jeremy-daily/Teensy-Crash-EDR/docs/images/2016-09-08 15.51.45.jpg

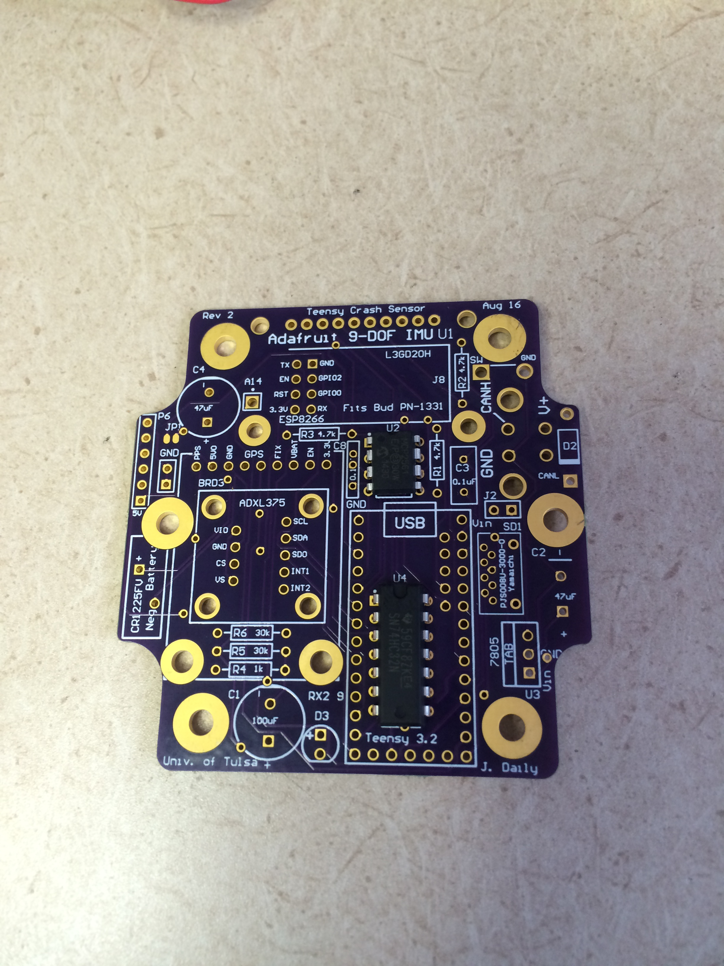
docs/images/2016-09-08 15.51.45.jpg
