jeremy-daily/Teensy-Crash-EDR/docs/images/2016-09-08 15.54.55.jpg

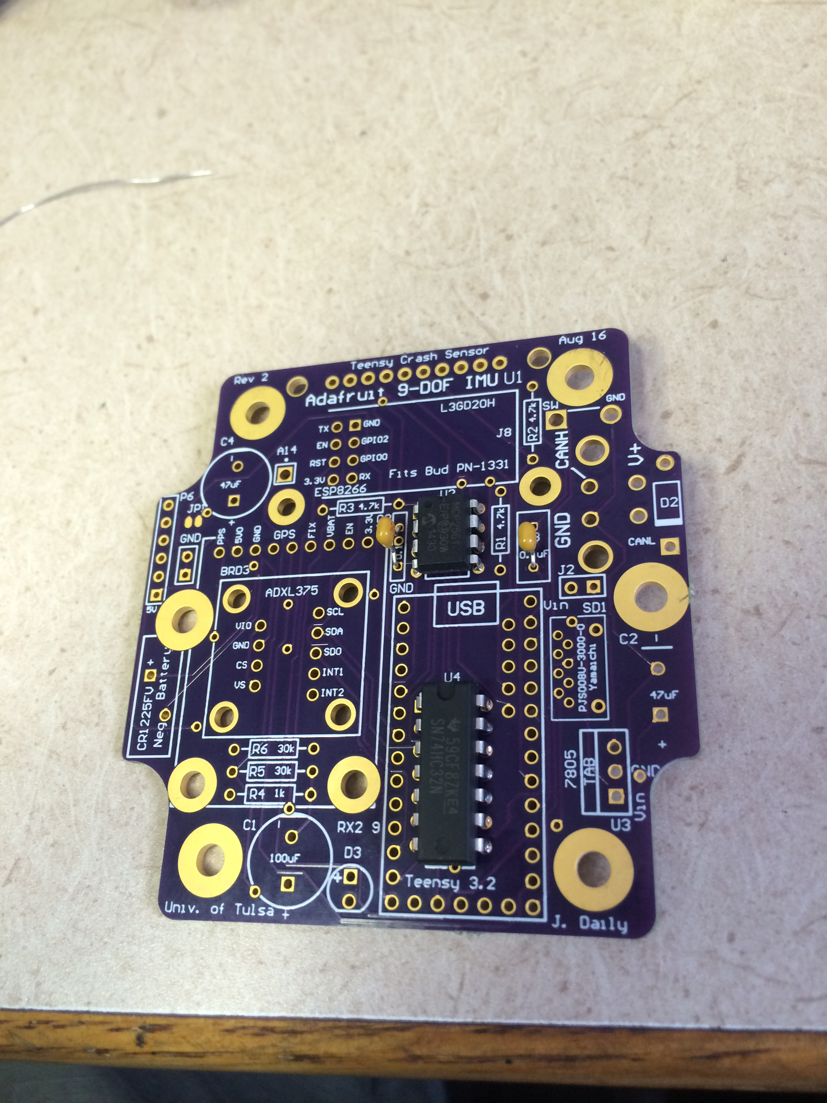
docs/images/2016-09-08 15.54.55.jpg
