jeremy-daily/Teensy-Crash-EDR/docs/images/2016-09-08 16.11.41.jpg

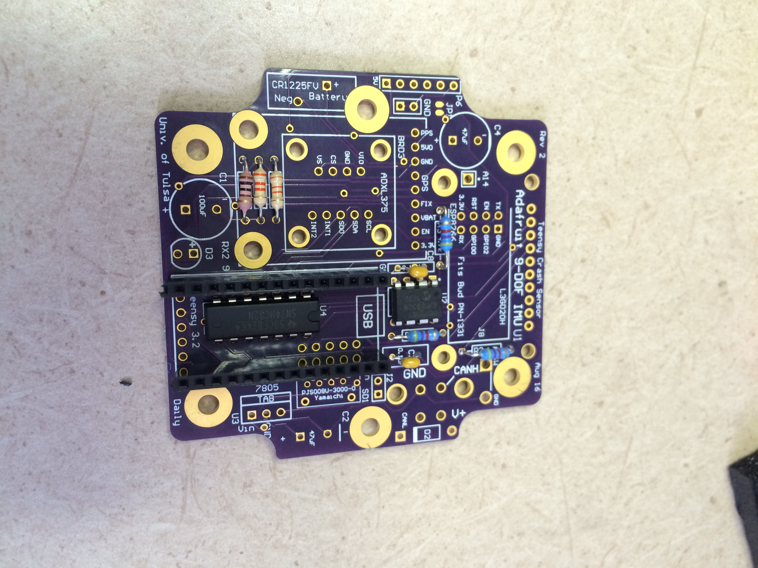
docs/images/2016-09-08 16.11.41.jpg
