jeremy-daily/Teensy-Crash-EDR/docs/images/2016-09-08 16.32.50.jpg

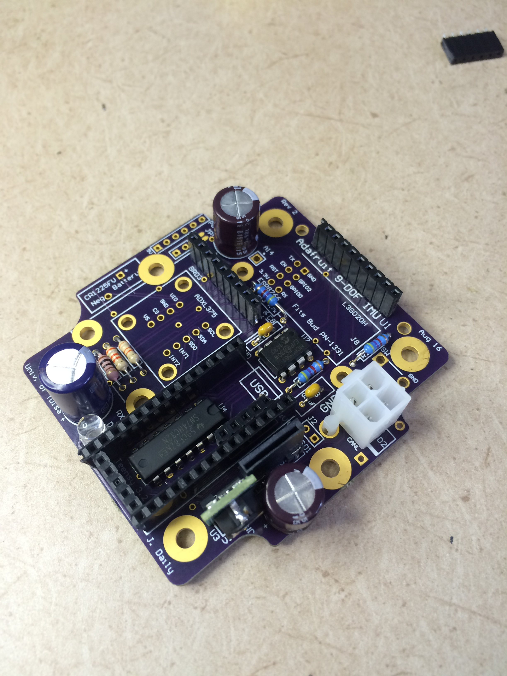
docs/images/2016-09-08 16.32.50.jpg
