jeremy-daily/Teensy-Crash-EDR/docs/images/2016-09-08 16.55.00.jpg

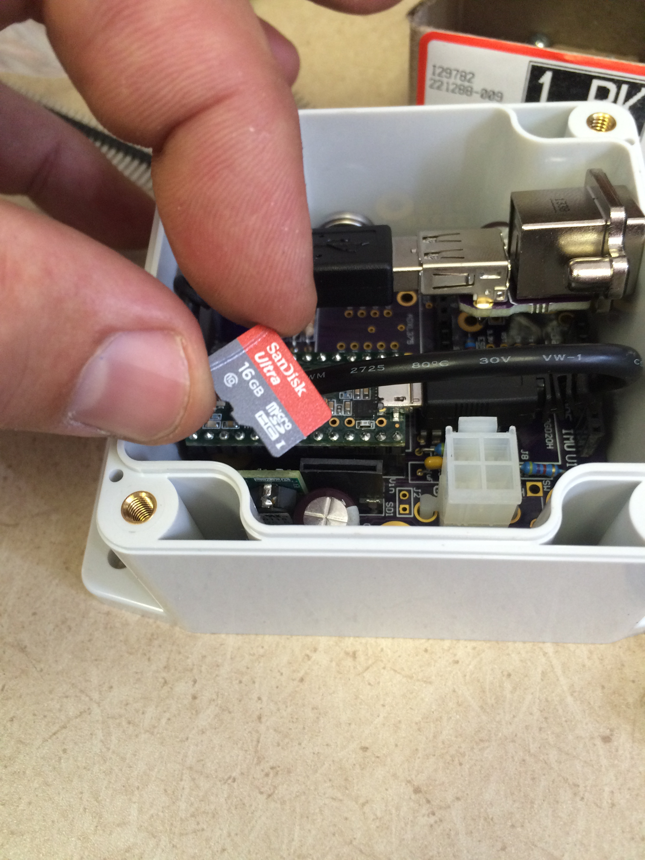
docs/images/2016-09-08 16.55.00.jpg
