jeremy-daily/Teensy-Crash-EDR/docs/images/2016-09-09 11.59.14.jpg

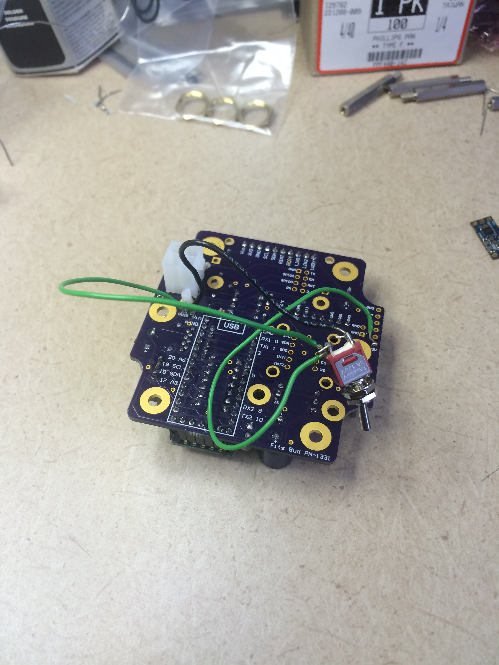
docs/images/2016-09-09 11.59.14.jpg
