jeremy-daily/Teensy-Crash-EDR/docs/images/2016-09-09 12.16.07.jpg

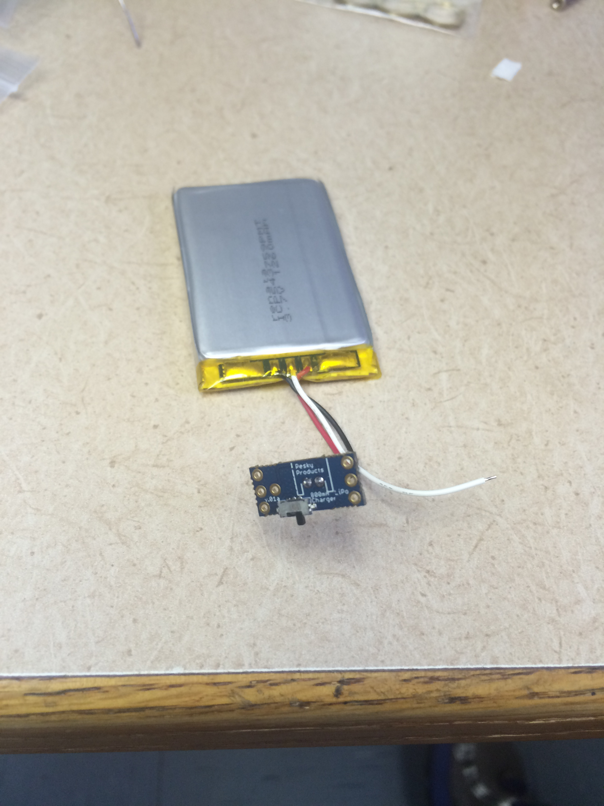
docs/images/2016-09-09 12.16.07.jpg
