jeremy-daily/Teensy-Crash-EDR/docs/images/2016-09-09 12.16.24.jpg

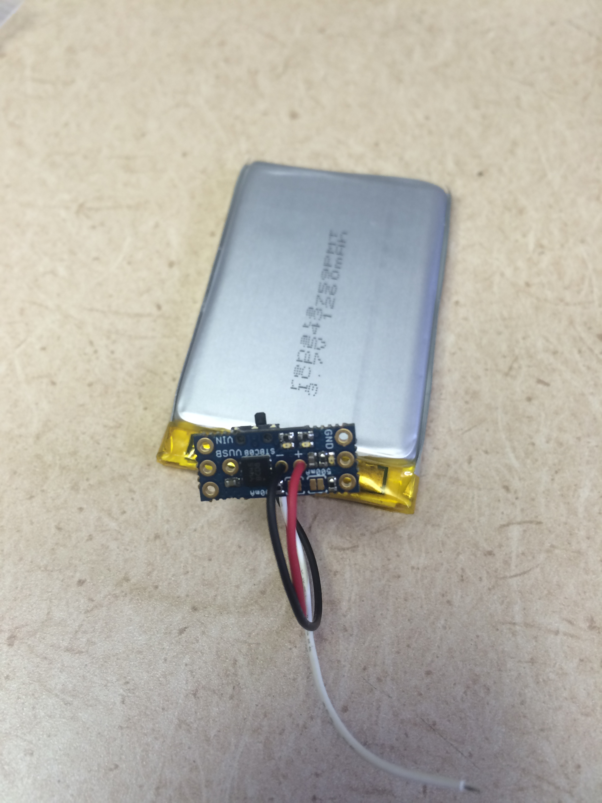
docs/images/2016-09-09 12.16.24.jpg
