jeremy-daily/Teensy-Crash-EDR/docs/images/2016-09-09 12.26.00.jpg

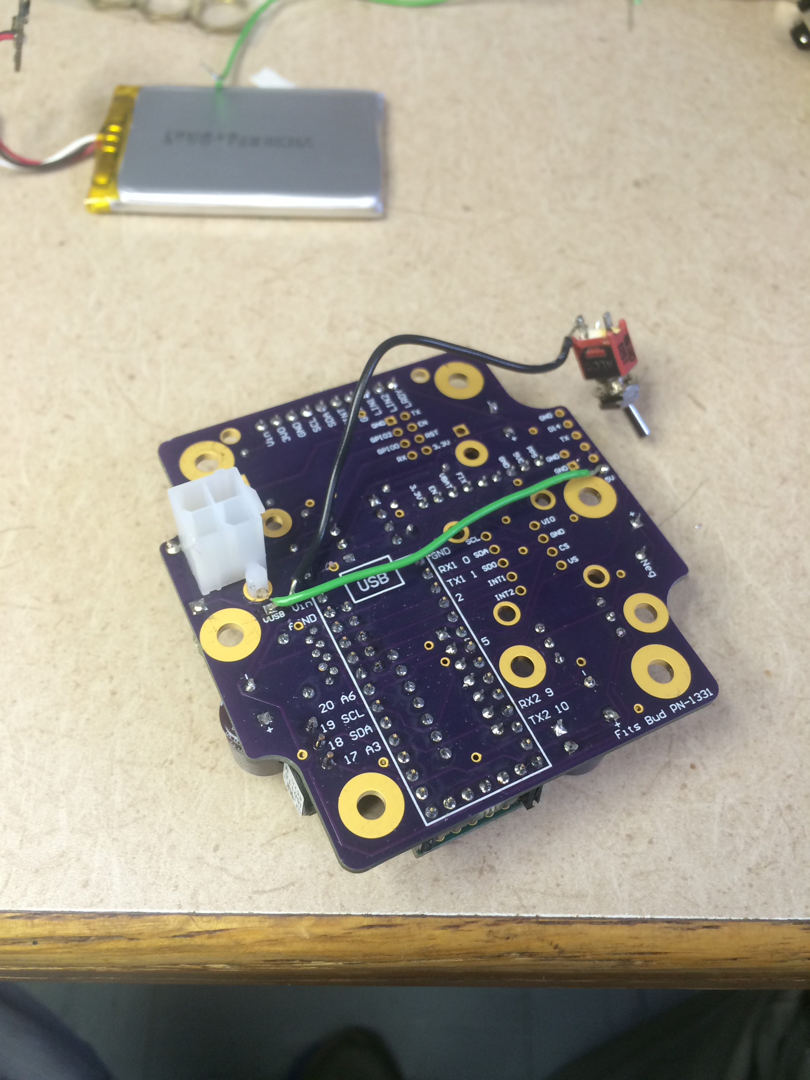
docs/images/2016-09-09 12.26.00.jpg
