jeremy-daily/Teensy-Crash-EDR/docs/images/2016-09-09 12.34.02.jpg

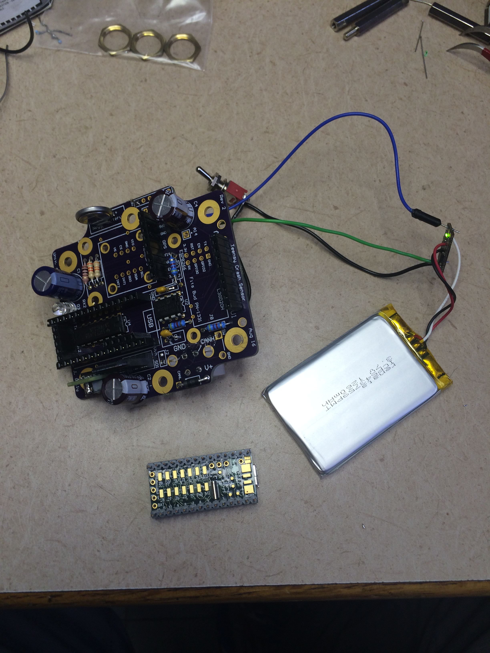
docs/images/2016-09-09 12.34.02.jpg
