jeremy-daily/Teensy-Crash-EDR/docs/images/2016-09-09 12.36.15.jpg

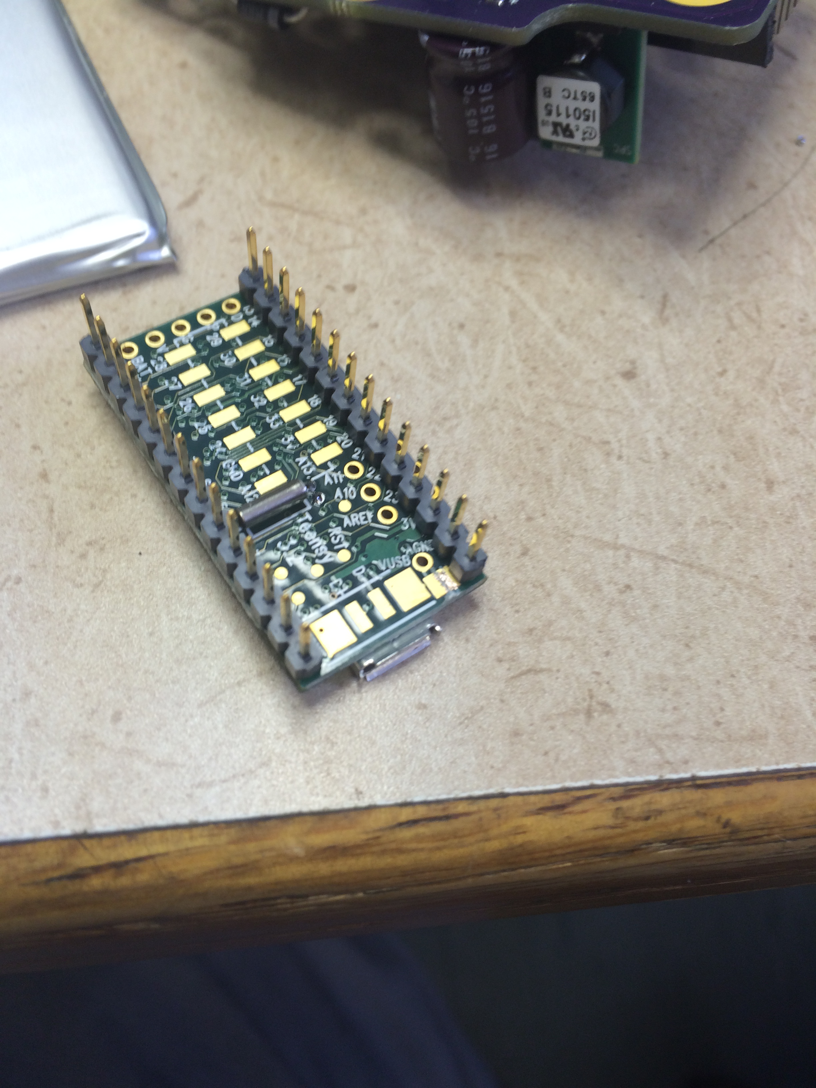
docs/images/2016-09-09 12.36.15.jpg
