jeremy-daily/Teensy-Crash-EDR/docs/images/2016-09-09 13.00.01.jpg

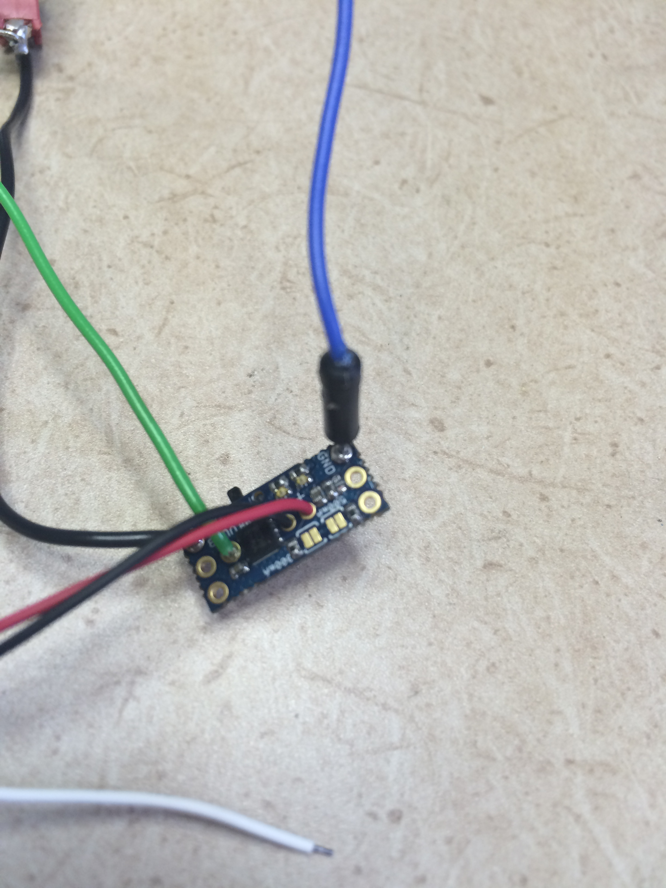
docs/images/2016-09-09 13.00.01.jpg
