jeremy-daily/Teensy-Crash-EDR/docs/images/2016-09-09 13.43.51.jpg

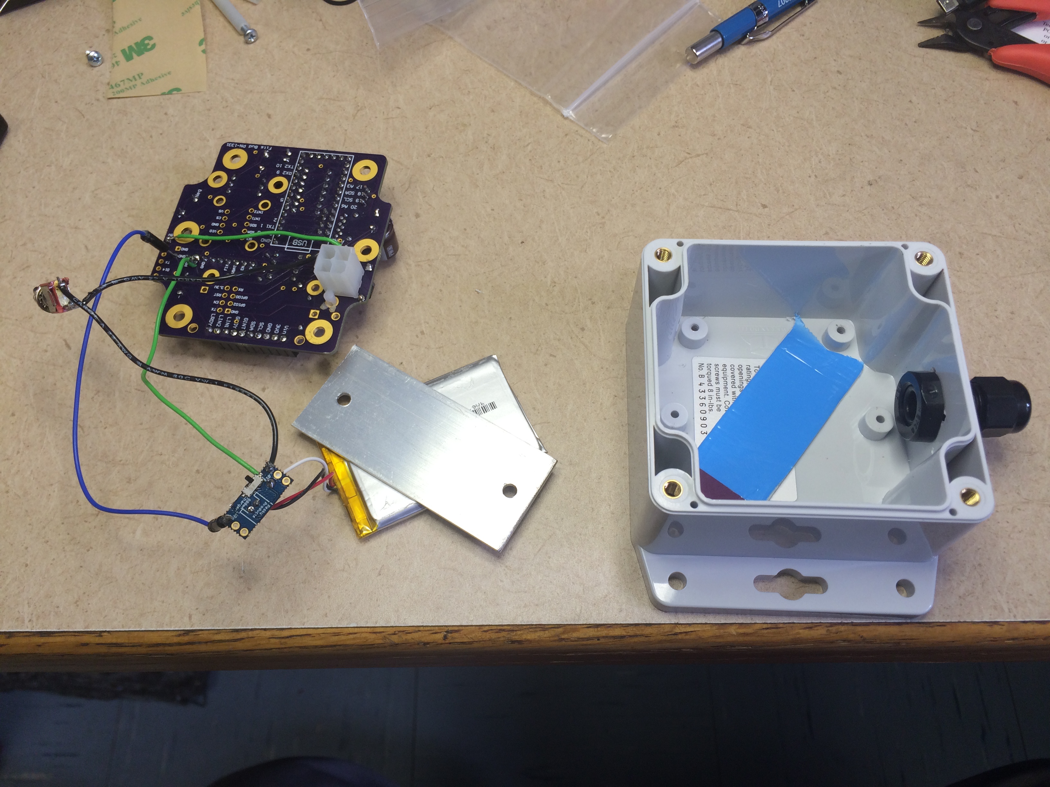
docs/images/2016-09-09 13.43.51.jpg
