jeremy-daily/Teensy-Crash-EDR/docs/images/2016-09-09 13.45.09.jpg

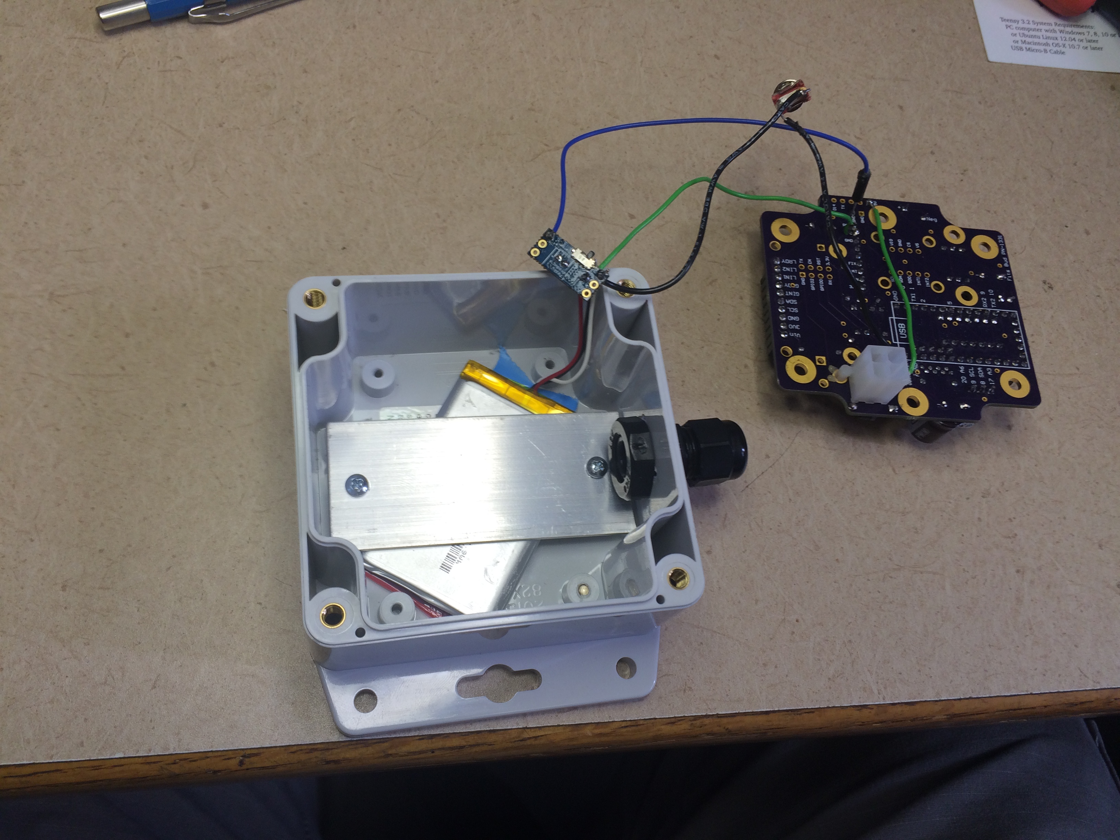
docs/images/2016-09-09 13.45.09.jpg
