jeremy-daily/Teensy-Crash-EDR/docs/images/2016-09-09 13.49.27.jpg

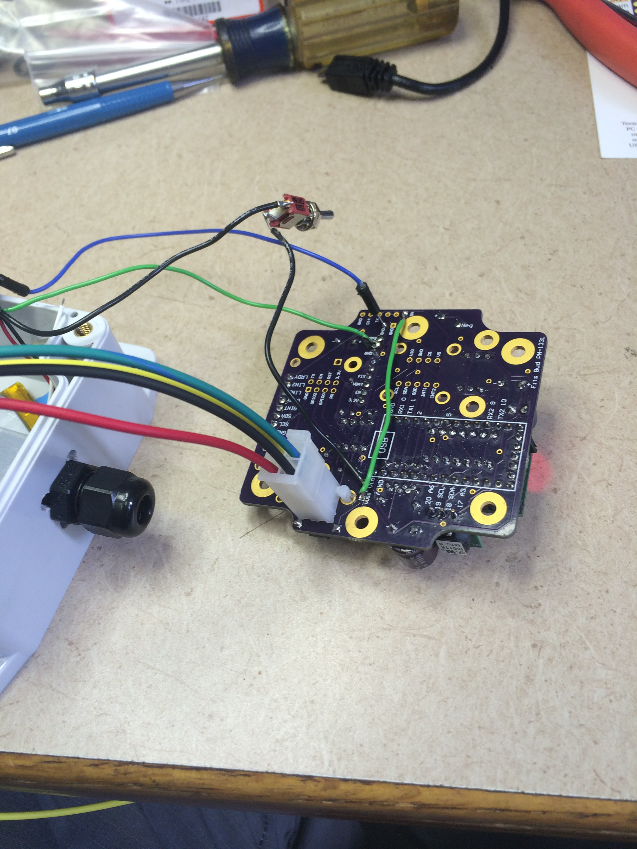
docs/images/2016-09-09 13.49.27.jpg
