jeremy-daily/Teensy-Crash-EDR/docs/images/2016-09-09 14.00.38.jpg

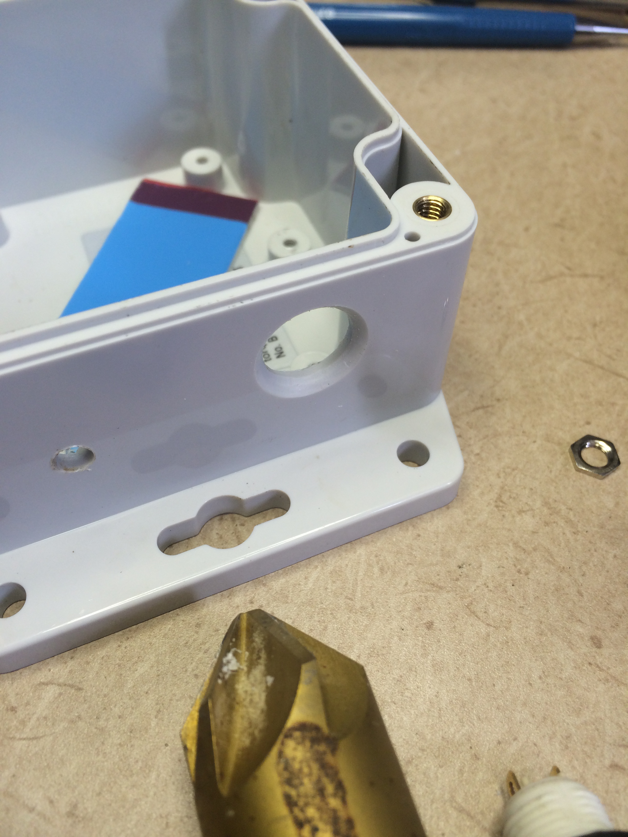
docs/images/2016-09-09 14.00.38.jpg
