jeremy-daily/Teensy-Crash-EDR/docs/images/2016-09-09 14.05.18.jpg

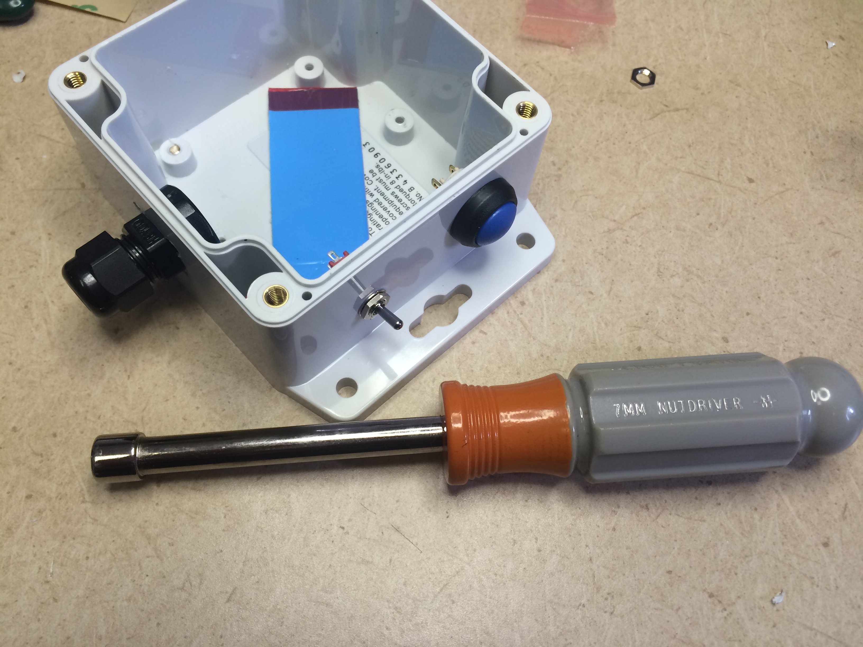
docs/images/2016-09-09 14.05.18.jpg
