jeremy-daily/Teensy-Crash-EDR/docs/images/2016-09-09 14.09.20.jpg

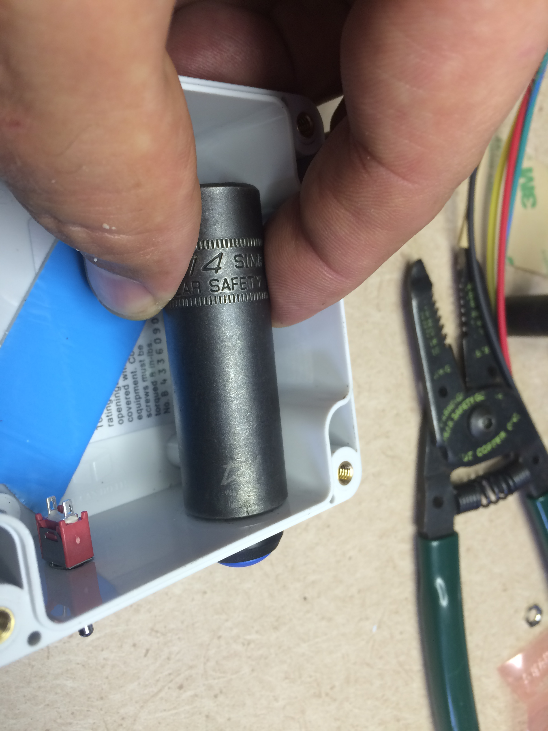
docs/images/2016-09-09 14.09.20.jpg
