jeremy-daily/Teensy-Crash-EDR/docs/images/2016-09-09 15.44.33.jpg

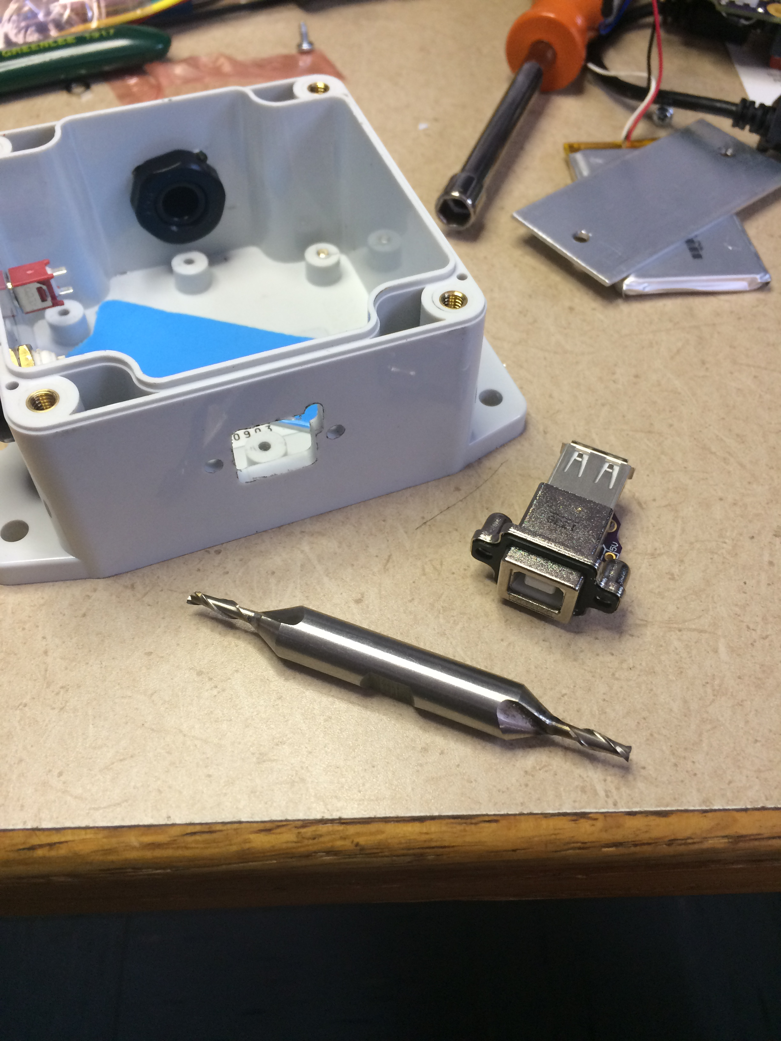
docs/images/2016-09-09 15.44.33.jpg
