jeremy-daily/Teensy-Crash-EDR/docs/images/2016-09-09 15.50.09.jpg

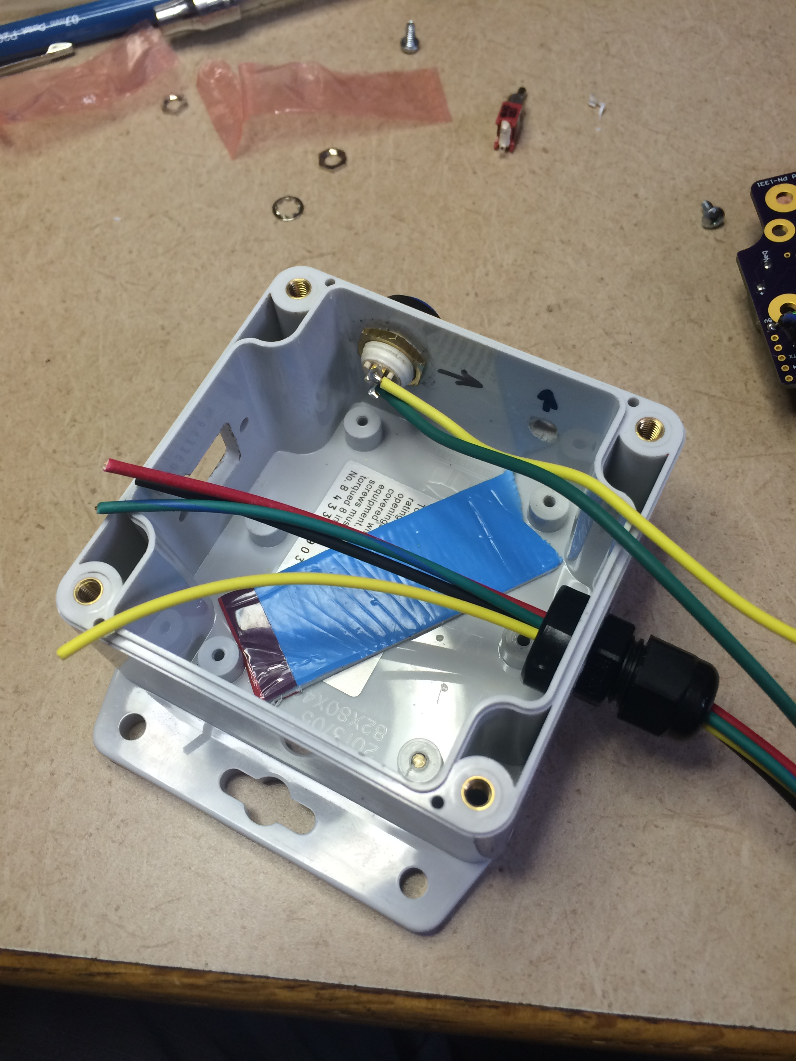
docs/images/2016-09-09 15.50.09.jpg
