jeremy-daily/Teensy-Crash-EDR/docs/images/2016-09-09 15.57.11.jpg

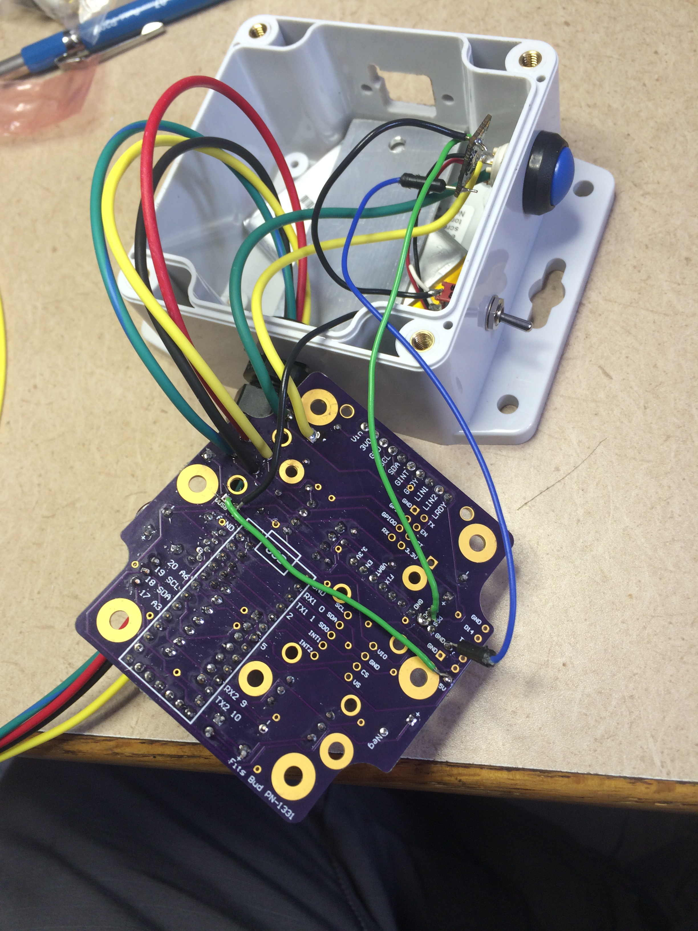
docs/images/2016-09-09 15.57.11.jpg
