jeremy-daily/Teensy-Crash-EDR/docs/images/2016-09-09 15.58.31.jpg

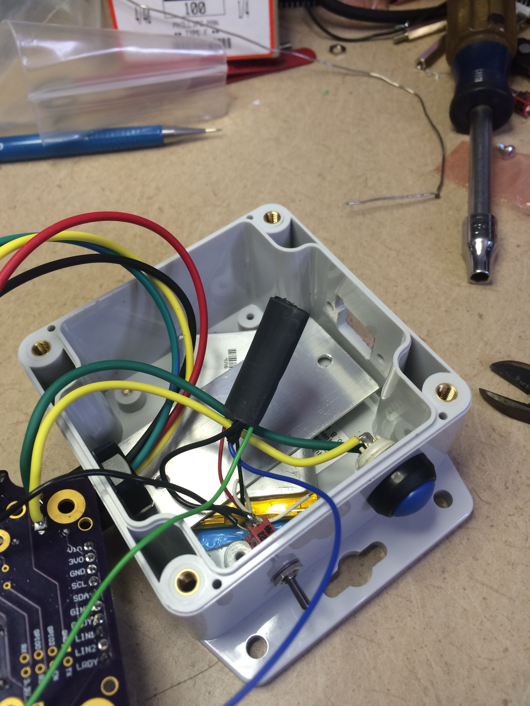
docs/images/2016-09-09 15.58.31.jpg
