jeremy-daily/Teensy-Crash-EDR/docs/images/2016-09-09 16.00.55.jpg

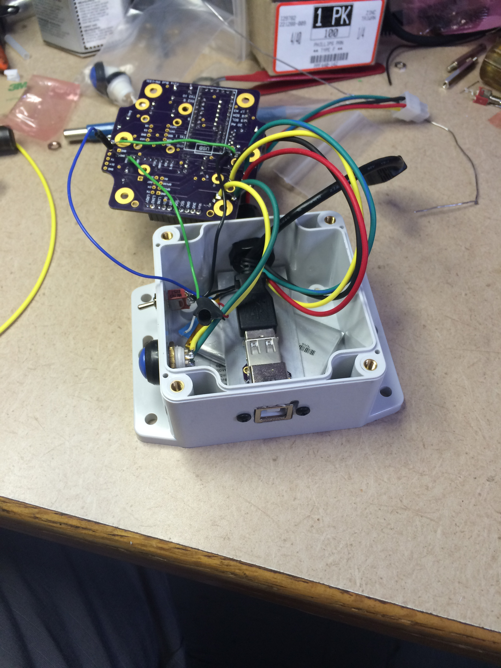
docs/images/2016-09-09 16.00.55.jpg
