jeremy-daily/Teensy-Crash-EDR/docs/images/2016-09-09 16.04.29.jpg

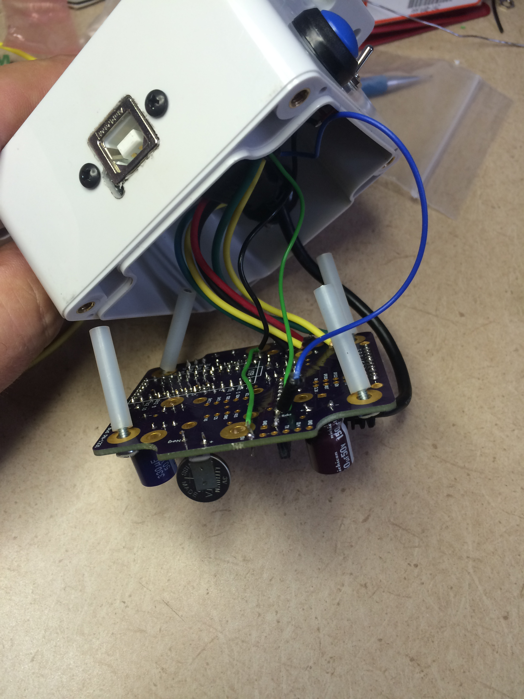
docs/images/2016-09-09 16.04.29.jpg
