jeremy-daily/Teensy-Crash-EDR/docs/images/2016-09-09 16.16.41.jpg

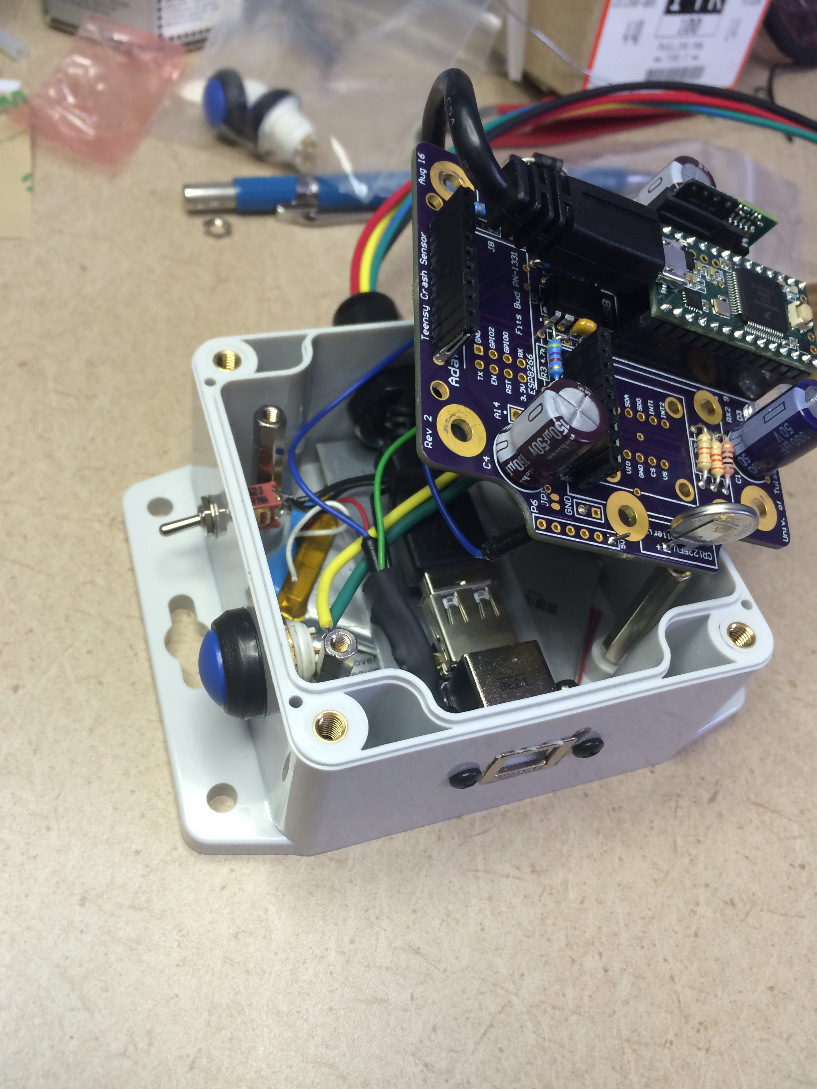
docs/images/2016-09-09 16.16.41.jpg
