jeremy-daily/Teensy-Crash-EDR/docs/images/2016-09-09 16.35.43.jpg

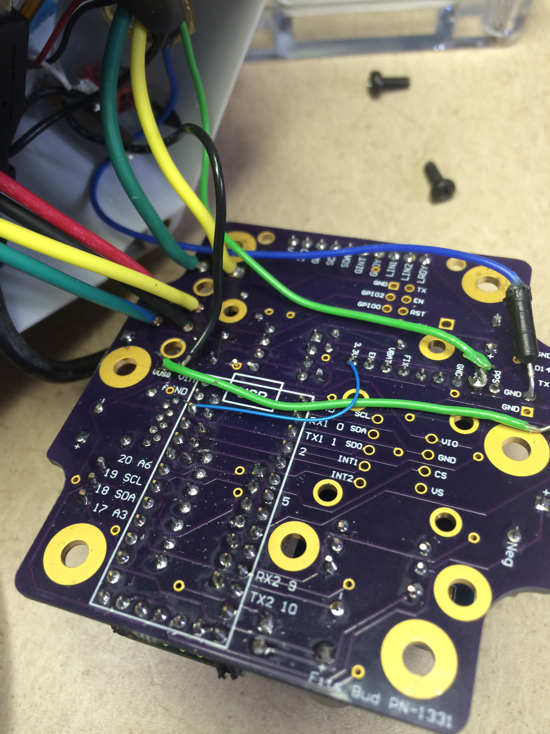
docs/images/2016-09-09 16.35.43.jpg
