jeremy-daily/Teensy-Crash-EDR/docs/images/2016-09-10 16.01.12.jpg

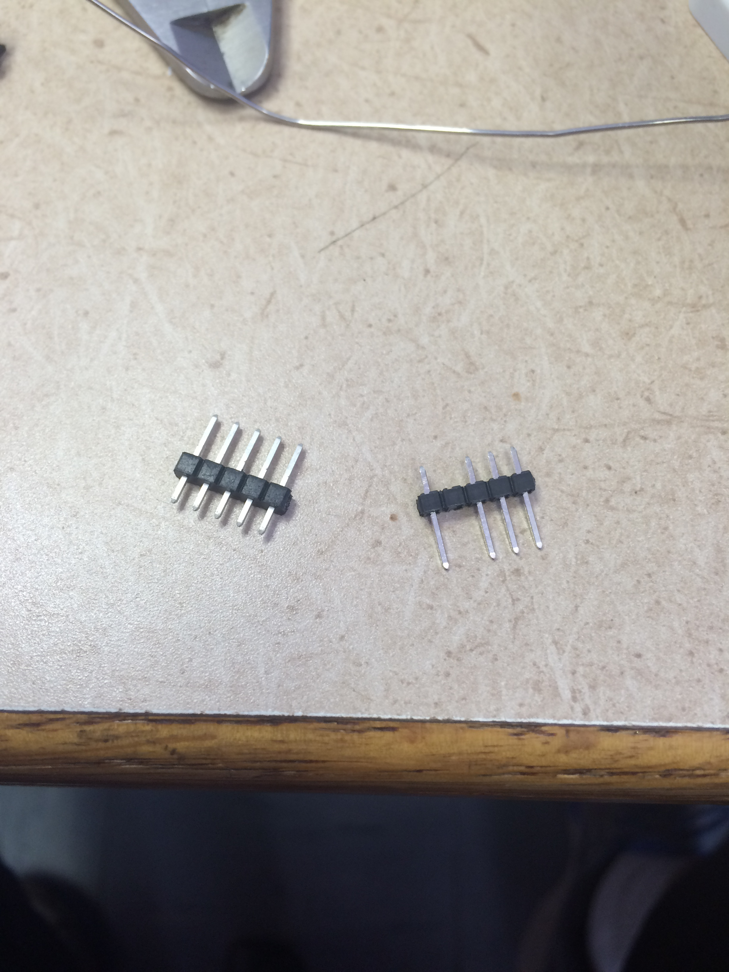
docs/images/2016-09-10 16.01.12.jpg
