jeremy-daily/Teensy-Crash-EDR/docs/images/2016-09-10 16.40.21.jpg

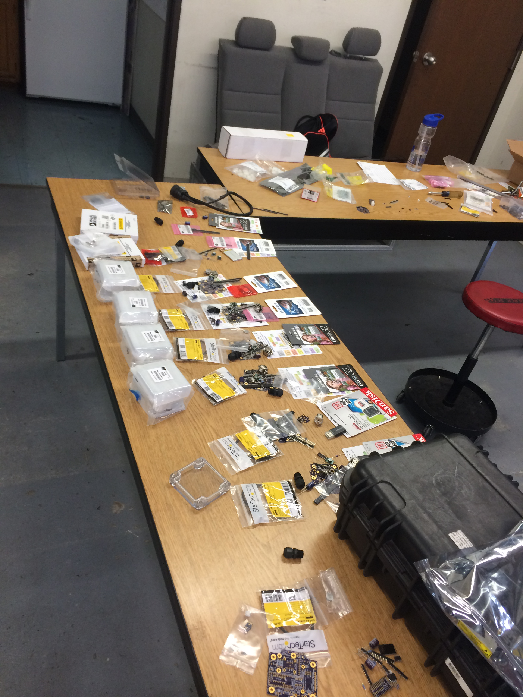
docs/images/2016-09-10 16.40.21.jpg
