jeremy-daily/Teensy-Crash-EDR/docs/images/2016-09-10 16.44.40.jpg

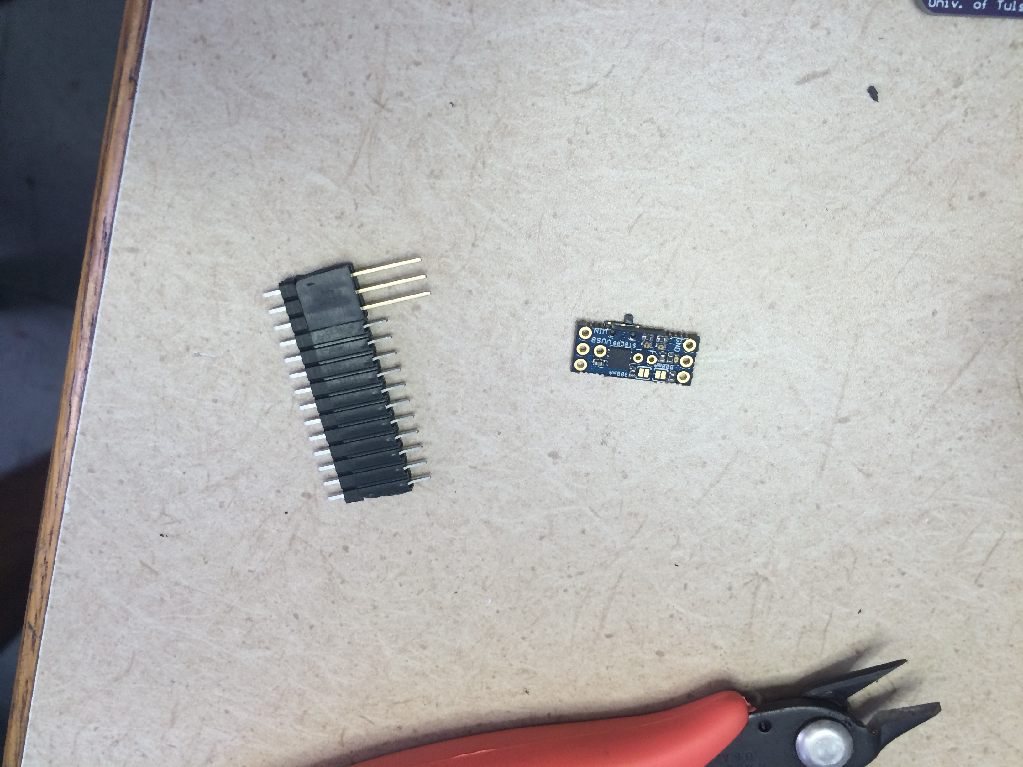
docs/images/2016-09-10 16.44.40.jpg
