jeremy-daily/Teensy-Crash-EDR/docs/images/BatteryMountedOntheBottom.jpg

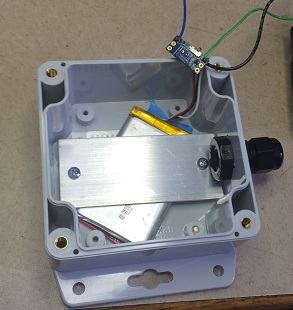
docs/images/BatteryMountedOntheBottom.jpg
