jeremy-daily/Teensy-Crash-EDR/_06_Low_Latency_CAN_Logger/UserDataType.h

#ifndef UserDataType_h
#define UserDataType_h
struct data_t {
  uint8_t type;
  uint8_t DLC;
  time_t timeStamp;
  uint32_t usec;
  uint32_t ID;
  uint8_t dataField[8];
  
};
#endif  // UserDataType_h
